guilhermecv/PI2/arduino_files/main/machine.ino

#include "machine.h"

void machine_init(void)
{
  TCCR2A  =   (1 << WGM21) | (0 << WGM20)         // Timer 2 in Mode 2 = CTC (clear on compar  e)
              | (0 << COM2A1) | (0 << COM2A0)         // do nothing with OC2A
              | (0 << COM2B1) | (0 << COM2B0);        // do nothing with OC2B
  TCCR2B  =   (0 << WGM22)                        // Timer 0 in Mode 2 = CTC (clear on compar  e)
              | (0 << FOC0A) | (0 << FOC0B)           // dont force outputs
              | (1 << CS22)                           // clock enabled, prescaller = 1024
              | (1 << CS21)
              | (1 << CS20);
  OCR2A   =   250;                                // Valor para igualdade de comparacao A par  a frequencia de 150 Hz  (80 - original)
  TIMSK2 |=   (1 << OCIE2A);                      // Ativa a interrupcao na igualdade de comp  aração do TC2 com OCR2A

  state_machine = INITIALIZING;

  sensor0 = sensor1 = 0;
}

void set_state_idle()
{
  state_machine = IDLE;
  VERBOSE_MSG_MACHINE(Serial.print("IDLE state\n"));
}

void set_state_running()
{
  state_machine = RUNNING;
  VERBOSE_MSG_MACHINE(Serial.print("RUNNING state\n"));
}

void set_state_error()
{
  state_machine = ERROR;
  VERBOSE_MSG_MACHINE(Serial.print("ERROR state\n"));
}
//############ TASKS ###############
void task_idle()
{
#ifdef LED_ON
  static uint8_t led_clk_div;
  if (led_clk_div++ > 50)
  {
    led_clk_div = 0;
    cpl_led();
  }
#endif

  // Sensor IR0 - Medição de volume
  if (sensor0)
  {
    set_state_running();
  }
}

void check_volume();

void task_error()
{
  VERBOSE_MSG_ERROR(Serial.print("Waiting for a reset\n"));

  for (;;)
  {
    cpl_led();
    cpl_buzzer();
    delay(100);
  }
}

//#################################
void machine_run()
{
  if (machine_clk)
  {
    machine_clk = 0;

    switch (state_machine)
    {
      case INITIALIZING:

        break;

      case IDLE:
        task_idle();
        break;

      case STEP0:
        check_volume();
        //                task_running();
        break;

      case ERROR:
        task_error();
        break;
    }
  }
}

ISR(TIMER2_COMPA_vect)
{
  machine_clk = 1;
}
