guilhermecv/PI2/Raspberry/firmware/mlx90614.c

#include "mlx90614.h"

/**
 * @brief Inicializa o sensor MLX90614
 */
void mlx_init()
{
	if (wiringPiSetup() == -1)
		exit(1);
	fd = wiringPiI2CSetup(MLX_I2CADDR);
}

/**
 * @brief Mede a temperatura ambiente
 */
float read_amb_temperature()
{
	fd = wiringPiI2CSetup(MLX_I2CADDR);
	return readTemp(MLX90614_TA);
}

/**
 * @brief Mede a temperatura do objeto em frente ao sensor
 */
float read_obj_temperature()
{
	fd = wiringPiI2CSetup(MLX_I2CADDR);
	return readTemp(MLX90614_TOBJ1);
}

/**
 * @brief Faz as conversões necessárias
 */
float readTemp(int reg)
{
	float temp;

	temp = read16(reg);
	temp *= .02;
	temp -= 273.15;

	return temp;
}

/**
 * @brief Faz a leitura dos registradores
 * @param a: registrador para leitura
 * @return : valor armazenado no registrador
 */
int read16(int a)
{
	int ret;
	wiringPiI2CWrite(fd, a); 				// Envia o endereço do registrador para leitura
	ret = wiringPiI2CReadReg16(fd,a);		// Recebe os dados
	return ret;
}
